Alonsog2/InputDeviceForDrawingTablet/MIDI.ino

//
// MIDI
//


void sendNoteOn_USB(byte pitch, byte velocity, byte channel) {               // Send noteOn 
  midiEventPacket_t midiPack = {0x09, 0x90 | (channel-1), pitch, velocity};  // MIDIUSB channels are form 0 to 15
  MidiUSB.sendMIDI(midiPack);
  MidiUSB.flush();
  displayMIDIInfo(0x90, pitch, velocity, channel);
}



void sendNoteOff_USB(byte pitch, byte velocity, byte channel ) {            // Send noteOff
  midiEventPacket_t midiPack = {0x08, 0x80 | (channel-1), pitch, velocity}; // MIDIUSB channels are form 0 to 15
  MidiUSB.sendMIDI(midiPack);
  MidiUSB.flush();
  displayMIDIInfo(0x80, pitch, velocity, channel);
}



void sendCtrlChange_USB(byte control, byte value, byte channel) {
  midiEventPacket_t event = {0x0B, 0xB0 | (channel-1), control, value};     // MIDIUSB channels are form 0 to 15
  MidiUSB.sendMIDI(event);
  MidiUSB.flush();
  displayMIDIInfo(0xB0, control, value, channel);
}



void sendMIDIreset(){
  midiEventPacket_t event = {0xFF, 0, 0, 0};
  MidiUSB.sendMIDI(event);
  MidiUSB.flush();
}



//This enum is defined in Setups/////////////////////////////////
//  MIDI_CHANNEL = 0,           // Channel (1-16/0=global)
//  MIDI_CC_OR_NOTE,            // CC or Note (0,1)
//  MIDI_MOMENTARY,             // momentary or toggle (0/1)
//  MIDI_nCC_OR_NOTEPITCH,      // nCC or NotePitch
//  MIDI_ValMin_OR_velNoteOff,  // valMinCC or noteOff
//  MIDI_ValMax_OR_velNoteOn

void pressedMIDIKey(byte acts[][MIDI_ACTIONS_STRUC_KEYS_count], int keyIndex){
  //Serial.println(F("Midi pressed")); 
  byte channel = (acts[keyIndex][MIDI_CHANNEL] == 0) ? GLOBAL_MIDI_CHANNEL : acts[keyIndex][MIDI_CHANNEL];

  if (acts[keyIndex][MIDI_CC_OR_NOTE] == 1) {                                               // Note
    boolean bSendNote = true;
    byte note = acts[keyIndex][MIDI_nCC_OR_NOTEPITCH];
    if  (acts[keyIndex][MIDI_MOMENTARY] != 0) {                                             // if toggle...
      bSendNote = toggleMIDInoteStatus(note);
      if (!bSendNote) {
        sendNoteOff_USB(note,acts[keyIndex][MIDI_ValMin_OR_velNoteOff], channel); 
      }
    }
    if  (bSendNote) {
      sendNoteOn_USB(note,acts[keyIndex][MIDI_ValMax_OR_velNoteOn], channel);      
    }
    
  } else {                                                                                         // CC 
    sendCtrlChange_USB(acts[keyIndex][MIDI_nCC_OR_NOTEPITCH],acts[keyIndex][MIDI_ValMax_OR_velNoteOn], channel);  
  }
}



boolean toggleMIDInoteStatus(byte note){  // toggle state and return the new state of the note
  byte datByte = MIDInoteStatus[note/8];
  byte mask = 1 << (note%8);
  boolean bNewStatusNote = ( (datByte & mask) == 0);
  if (bNewStatusNote) {
    datByte = datByte | mask;
  } else {
    datByte = datByte & (! mask);  
  }
  MIDInoteStatus[note/8] = datByte;
  return bNewStatusNote;
}



void releasedMIDIKey(byte acts[][MIDI_ACTIONS_STRUC_KEYS_count], int keyIndex){
  //Serial.println(F("Midi released")); 
  byte channel = (acts[keyIndex][MIDI_CHANNEL] == 0) ? GLOBAL_MIDI_CHANNEL : acts[keyIndex][MIDI_CHANNEL];
  if (acts[keyIndex][MIDI_CC_OR_NOTE] == 1) {                                                // Note
    if  (acts[keyIndex][MIDI_MOMENTARY] == 0) {                                              // Send NoteOff only if 'momentary' mode for this note
      sendNoteOff_USB(acts[keyIndex][MIDI_nCC_OR_NOTEPITCH],acts[keyIndex][MIDI_ValMin_OR_velNoteOff], channel);      
    }
  } else {                                                                                          // CC
    sendCtrlChange_USB(acts[keyIndex][MIDI_nCC_OR_NOTEPITCH],acts[keyIndex][MIDI_ValMin_OR_velNoteOff], channel);   
  }
}



void notePitch2Notation(byte pitch) {
  byte inx = 0;
  int octave = (pitch / 12) -1;           // octave from -1 to 9
  byte indexNote = (pitch % 12) *2 ;      // notes form 0=C to 11=B (the second char can be the sharp "#")
  buffNotation[inx++] = NOTE_NAMES[indexNote];
  buffNotation[inx++] = NOTE_NAMES[indexNote+1];
  if (octave < 0) {
    buffNotation[inx++] = '-';
  }
  buffNotation[inx++] = char(48+abs(octave));
  buffNotation[inx++] = 0;                // end string
}



void initMIDI() {
// whatever...
}
